tdunning/low-pass/images/qr.jpg

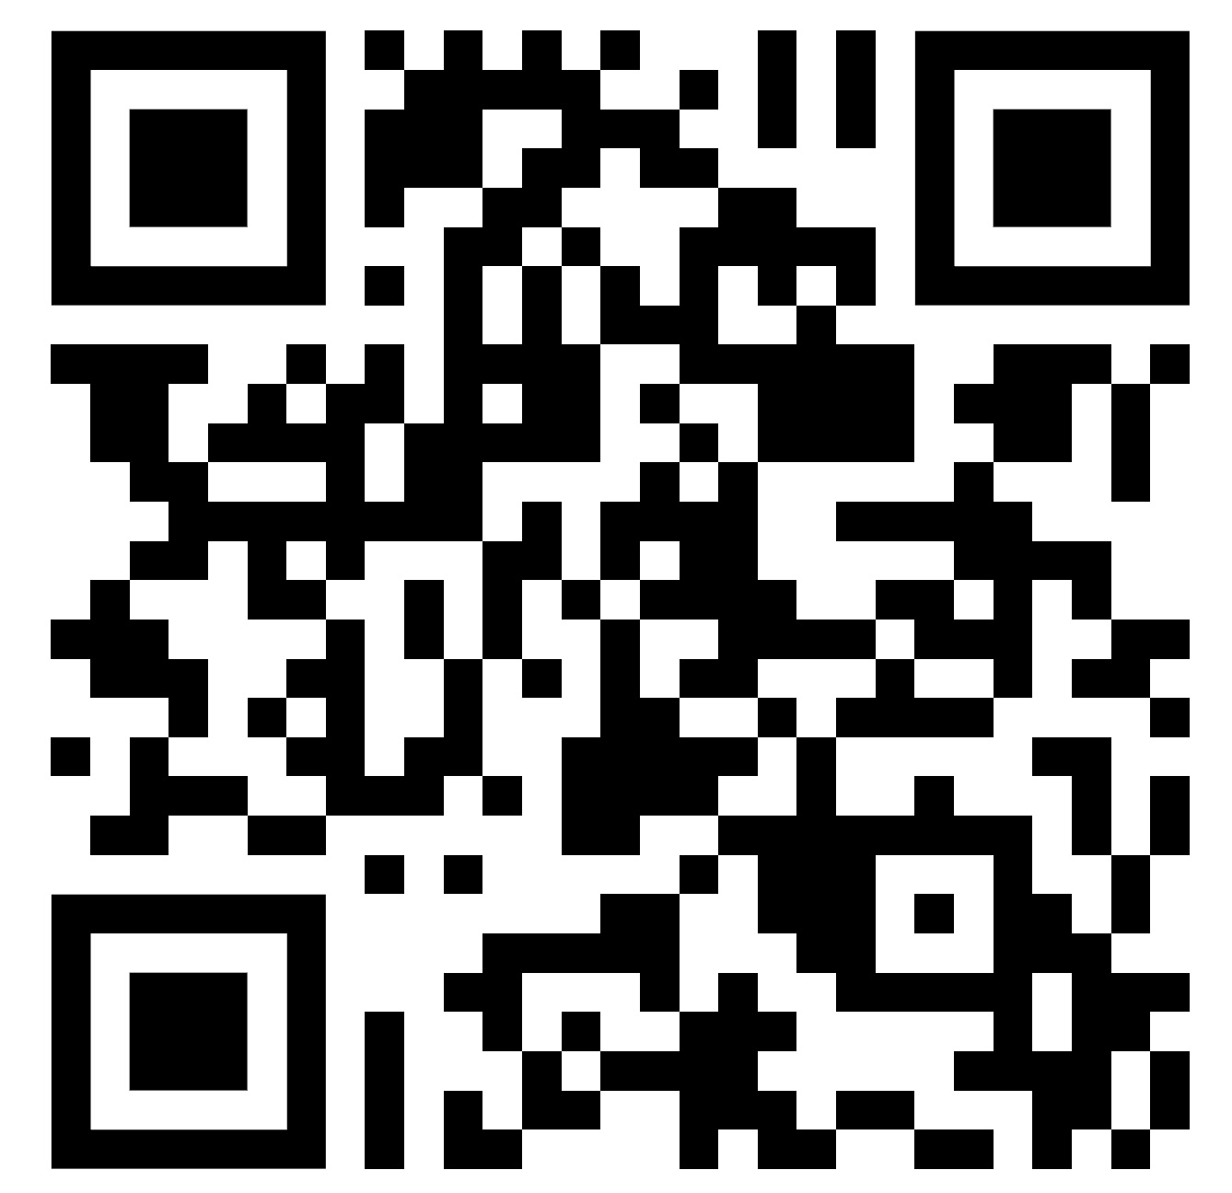
images/qr.jpg
